Frapais/Root-ESP32_Plant_Monitoring_Module/Photos/image1.jpg

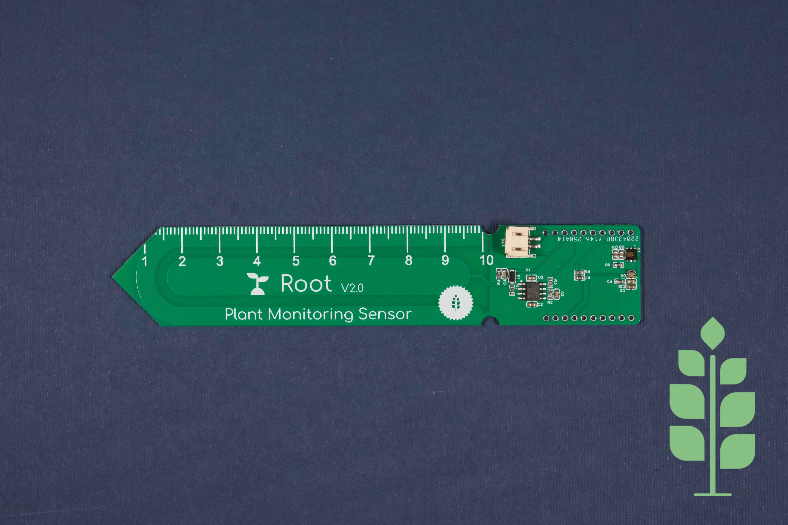
Photos/image1.jpg
