Frapais/Root-ESP32_Plant_Monitoring_Module/Photos/image2.jpg

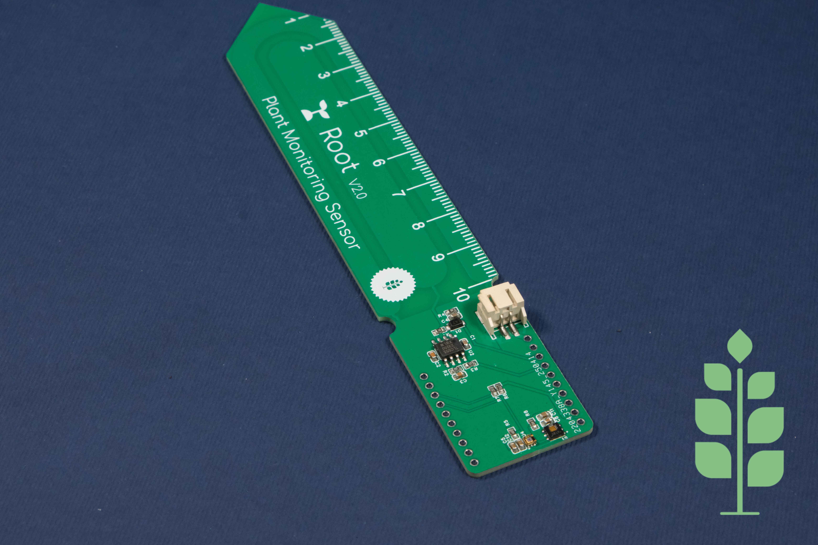
Photos/image2.jpg
