Frapais/Root-ESP32_Plant_Monitoring_Module/Photos/image3.jpg

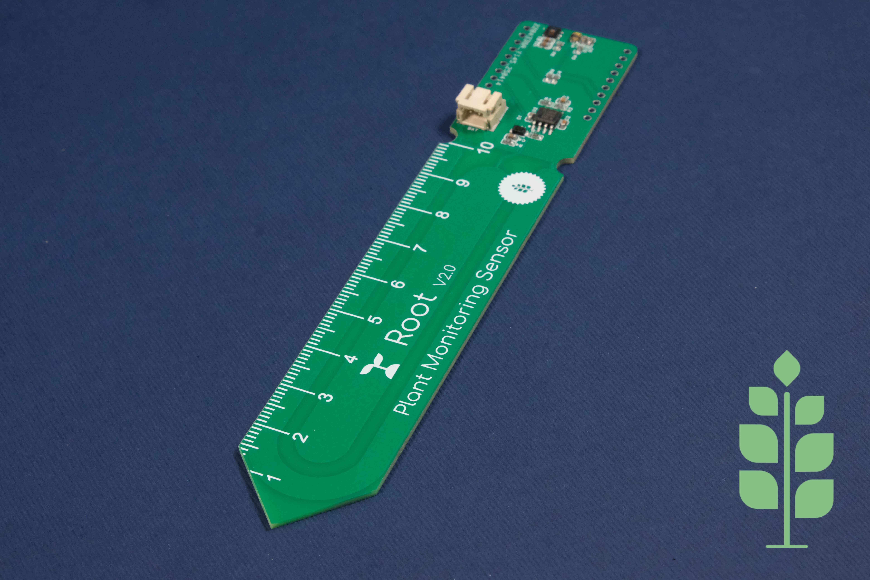
Photos/image3.jpg
