Frapais/Root-ESP32_Plant_Monitoring_Module/Photos/image4.jpg

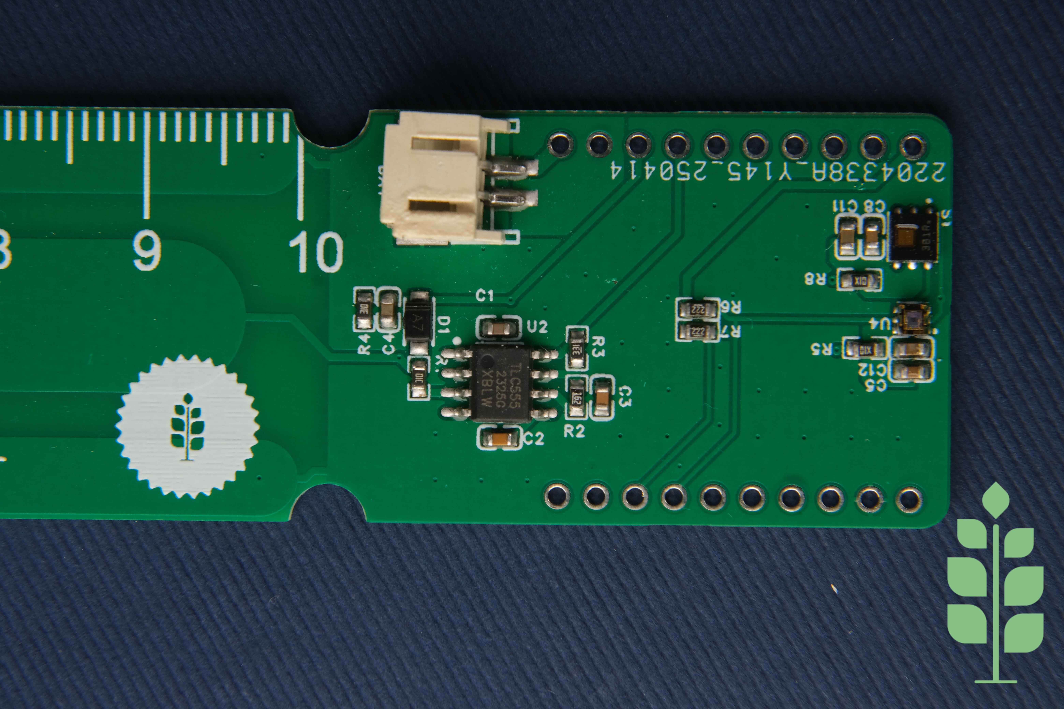
Photos/image4.jpg
