Frapais/Root-ESP32_Plant_Monitoring_Module/Photos/image5.jpg

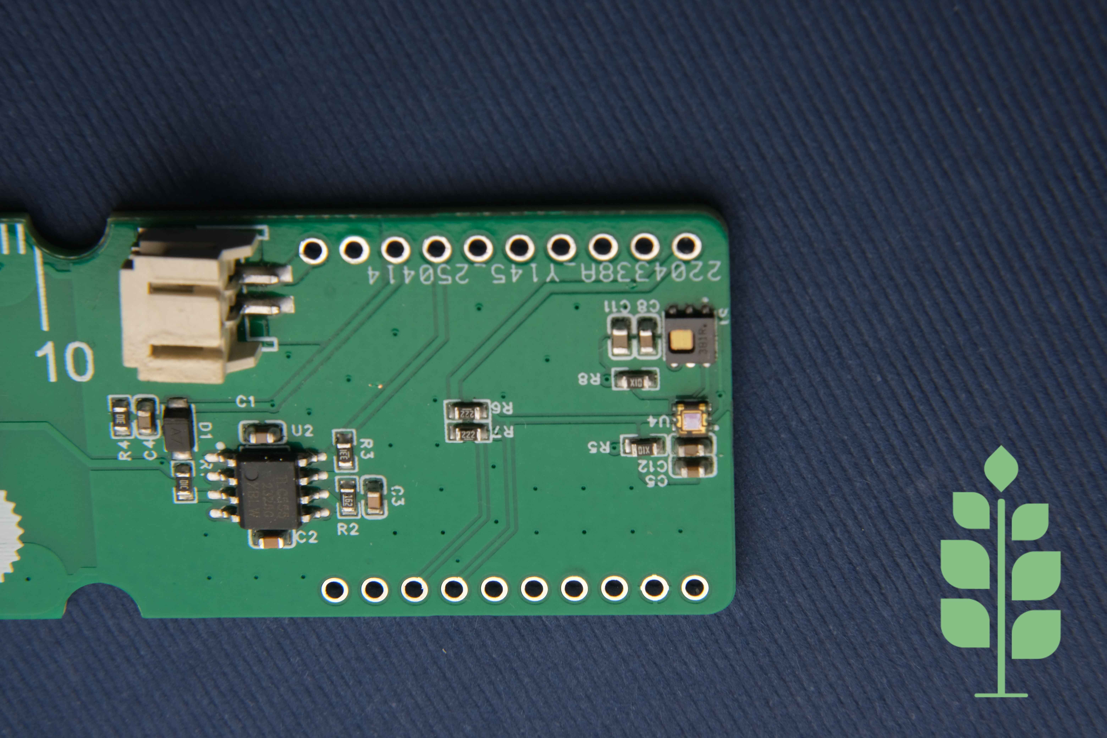
Photos/image5.jpg
