Frapais/Root-ESP32_Plant_Monitoring_Module/Photos/image7.jpg

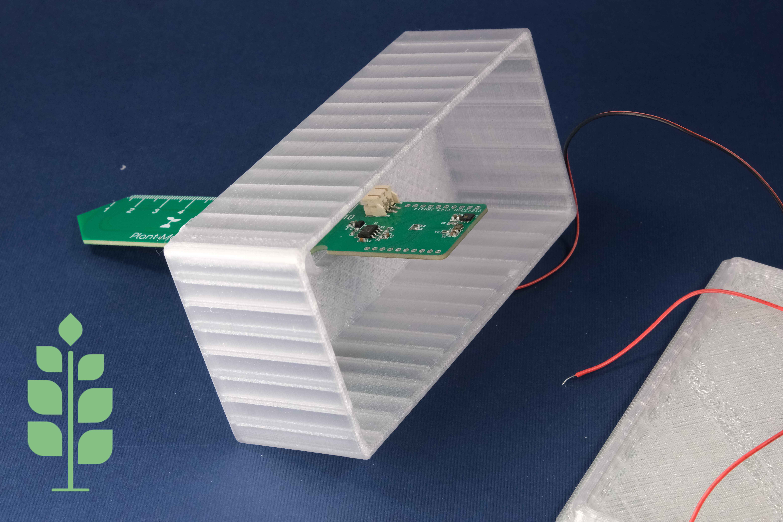
Photos/image7.jpg
