Frapais/Root-ESP32_Plant_Monitoring_Module/Photos/image8.jpg

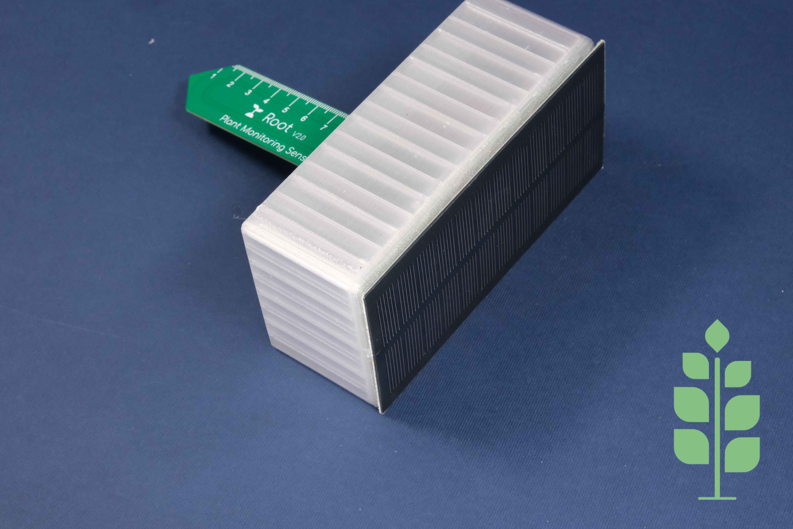
Photos/image8.jpg
