Frapais/Root-ESP32_Plant_Monitoring_Module/Photos/image9.jpg

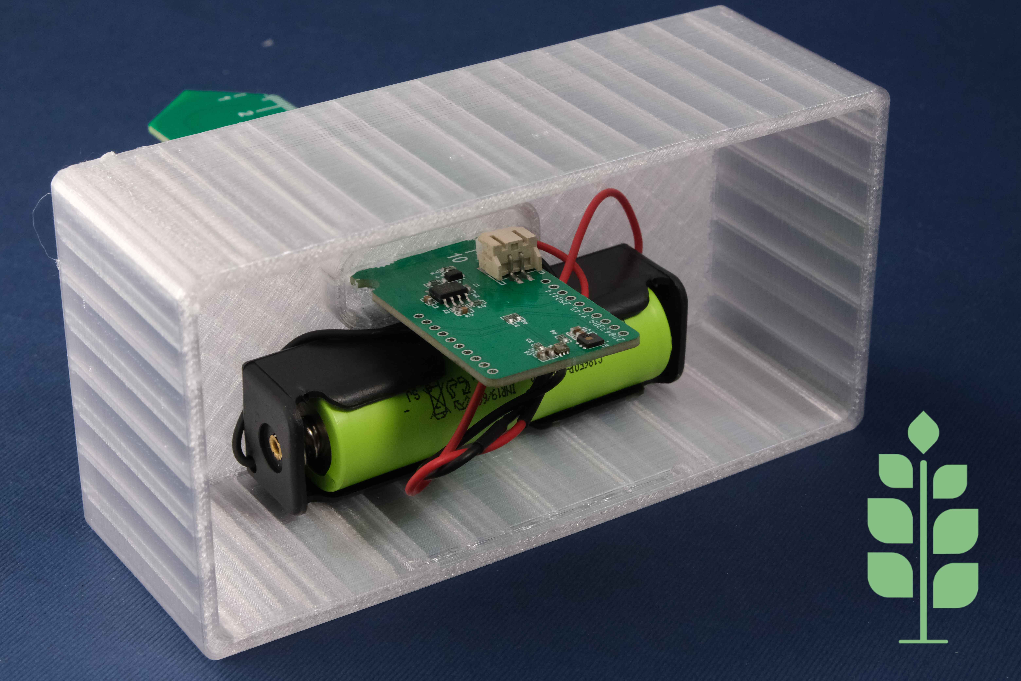
Photos/image9.jpg
