Frapais/Root-ESP32_Plant_Monitoring_Module/Photos/image10.jpg

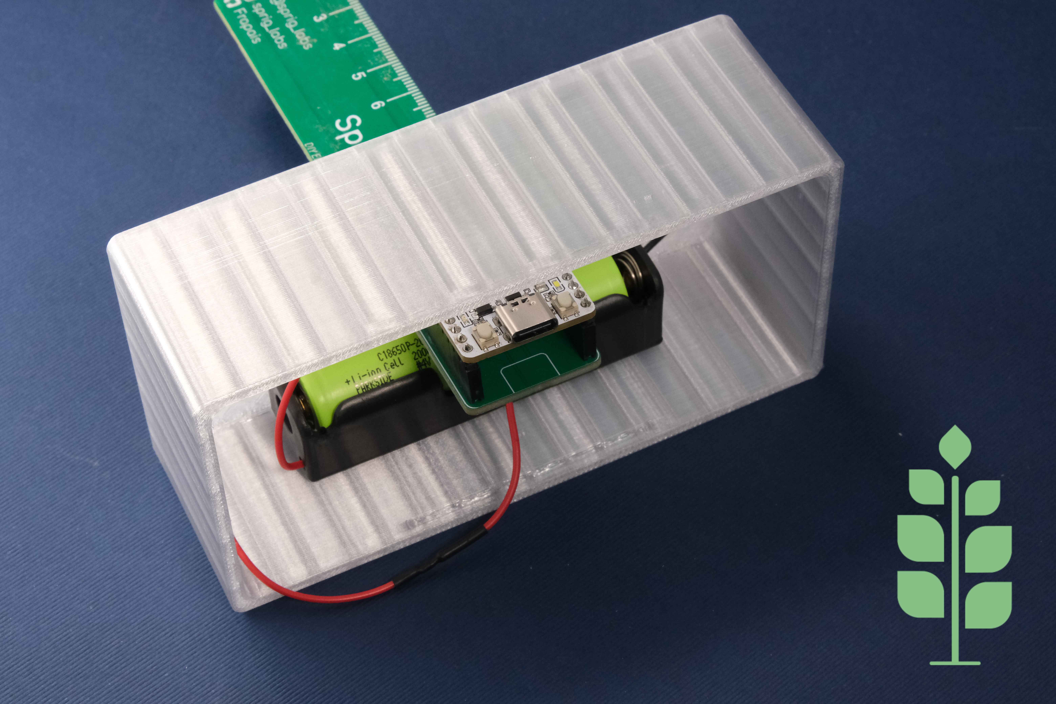
Photos/image10.jpg
